NightHawk32/esp32_wordclock/01_src/include/ota_manager.h

#ifndef OTA_MANAGER_H
#define OTA_MANAGER_H

#include <Arduino.h>

// Initialize both ArduinoOTA and ElegantOTA
void initOTA();

// Handle ArduinoOTA (call in loop)
void handleOTA();

#endif // OTA_MANAGER_H
