NightHawk32/esp32_wordclock/01_src/include/digits.h

typedef int digit_t[5][3];

digit_t digit0 = {
  {  1,  1,  1},
  {  1,  0,  1},
  {  1,  0,  1},
  {  1,  0,  1},
  {  1,  1,  1} 
};

digit_t digit1 = {
  {  0,  1,  0},
  {  0,  1,  0},
  {  0,  1,  0},
  {  0,  1,  0},
  {  0,  1,  0} 
};

digit_t digit2 = {
  {  1,  1,  1},
  {  0,  0,  1},
  {  1,  1,  1},
  {  1,  0,  0},
  {  1,  1,  1} 
};

digit_t digit3= {
  {  1,  1,  1},
  {  0,  0,  1},
  {  1,  1,  1},
  {  0,  0,  1},
  {  1,  1,  1} 
};

digit_t digit4 = {
  {  1,  0,  1},
  {  1,  0,  1},
  {  1,  1,  1},
  {  0,  0,  1},
  {  0,  0,  1} 
};

digit_t digit5 = {
  {  1,  1,  1},
  {  1,  0,  0},
  {  1,  1,  1},
  {  0,  0,  1},
  {  1,  1,  1} 
};

digit_t digit6 = {
  {  1,  1,  1},
  {  1,  0,  0},
  {  1,  1,  1},
  {  1,  0,  1},
  {  1,  1,  1} 
};

digit_t digit7 = {
  {  1,  1,  1},
  {  0,  0,  1},
  {  0,  0,  1},
  {  0,  0,  1},
  {  0,  0,  1} 
};

digit_t digit8 = {
  {  1,  1,  1},
  {  1,  0,  1},
  {  1,  1,  1},
  {  1,  0,  1},
  {  1,  1,  1} 
};

digit_t digit9 = {
  {  1,  1,  1},
  {  1,  0,  1},
  {  1,  1,  1},
  {  0,  0,  1},
  {  1,  1,  1} 
};
